grrd01/WordClock/Backend/2_features/3_Feature_Touch/3_Feature_Touch.ino

/*
 * ==================================================================================
 * TTP223 Touch Sensor an Wemos D1 mini
 * Verbindungsschema:
 * - 3.3V           -> VCC
 * - D5/GPIO14/SCLK -> I/O
 * - GND            -> GND
 * ==================================================================================
 */

const int TOUCH_PIN = D5; // Pin, an dem der Sensor hängt
const int LED_PIN = LED_BUILTIN; // Interne LED des Wemos

void setup() {
  pinMode(TOUCH_PIN, INPUT);
  pinMode(LED_PIN, OUTPUT);
}

void loop() {
  int touchState = digitalRead(TOUCH_PIN);

  if (touchState == HIGH) {
    digitalWrite(LED_PIN, LOW); // LED an (beim Wemos ist LOW = AN)
  } else {
    digitalWrite(LED_PIN, HIGH); // LED aus
  }
}
